kermitsgonnakermicide/ArrythmiX/images/img_1.png

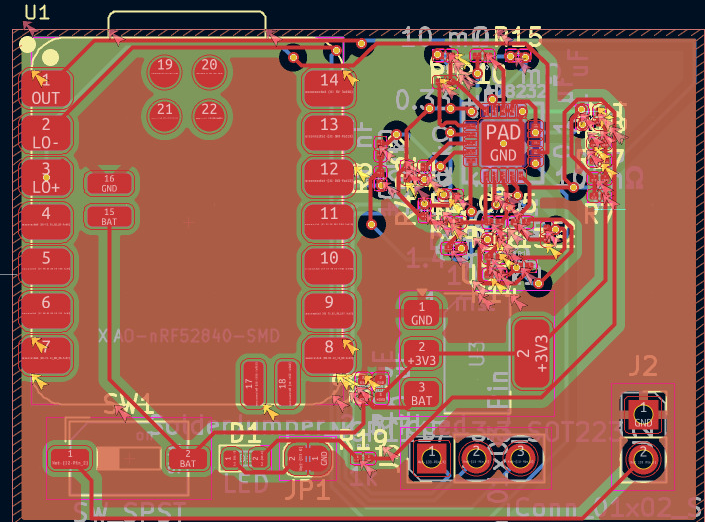
images/img_1.png
